RobertP1021/OpenBook/Images/Screenshot 2025-04-06 211312.png

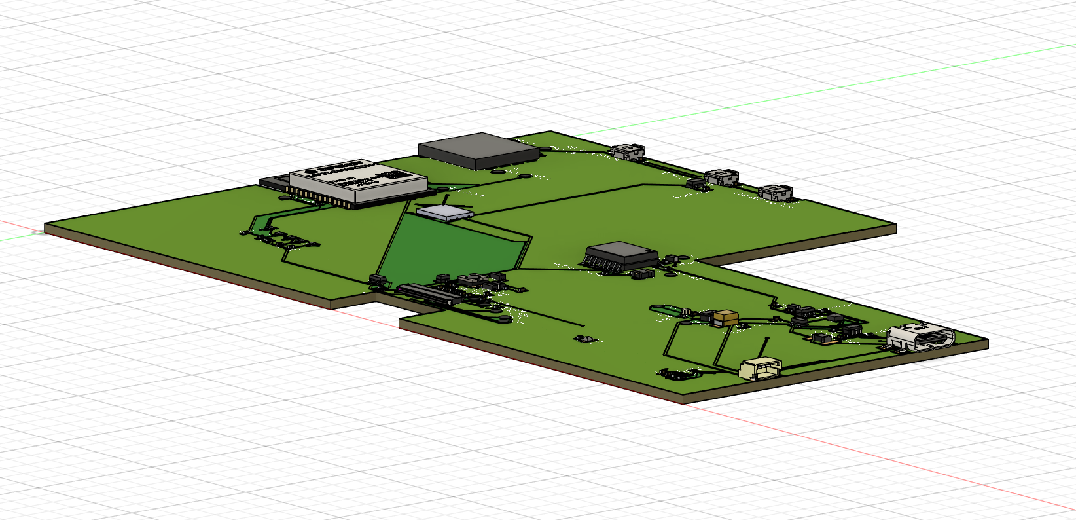
Images/Screenshot 2025-04-06 211312.png
